scribbledlife/boardkey/images/3D view for keybaord.png

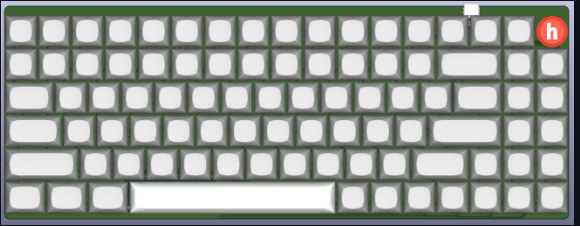
images/3D view for keybaord.png
