scribbledlife/boardkey/items/Screenshot 2026-02-18 142928.png

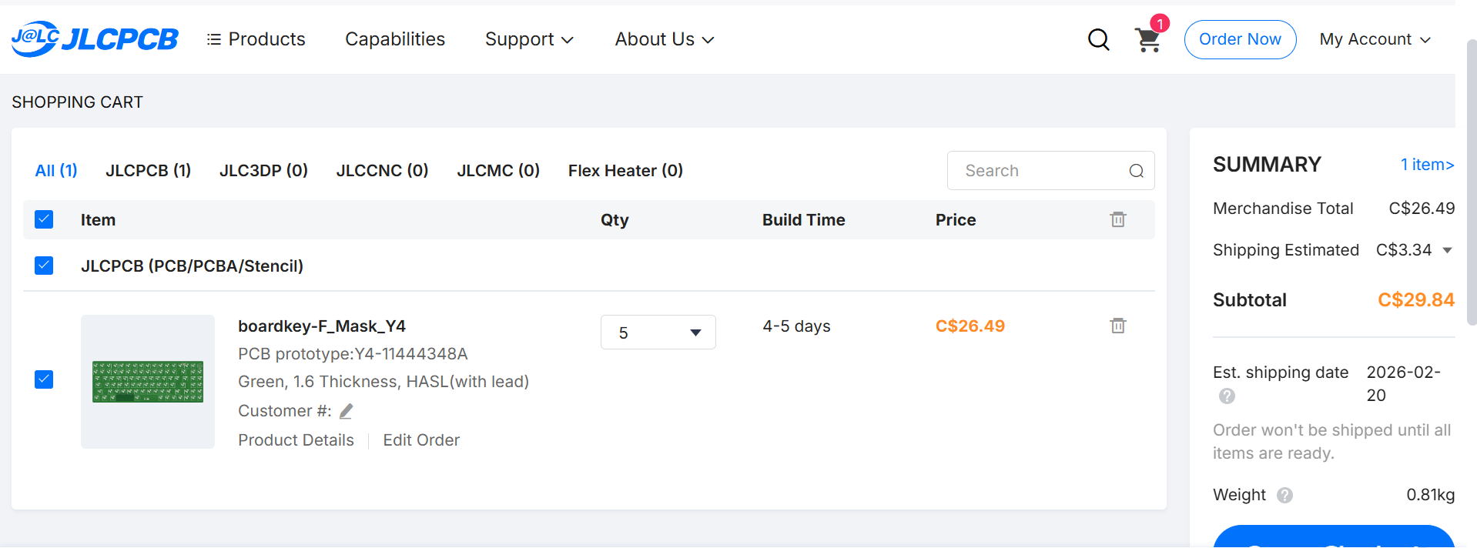
items/Screenshot 2026-02-18 142928.png
