scribbledlife/boardkey/items/Screenshot 2026-02-18 143510.png

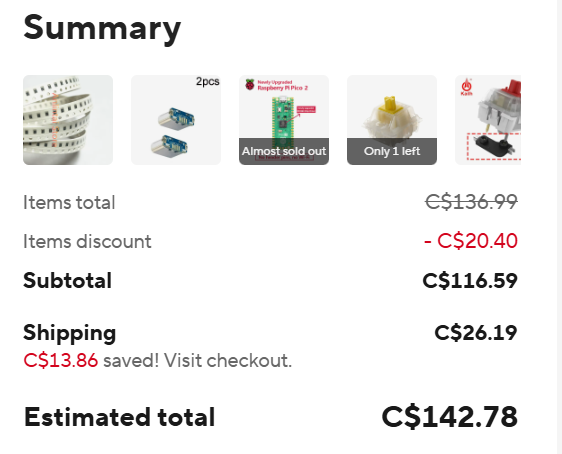
items/Screenshot 2026-02-18 143510.png
