scribbledlife/boardkey/items/Screenshot 2026-02-18 143522.png

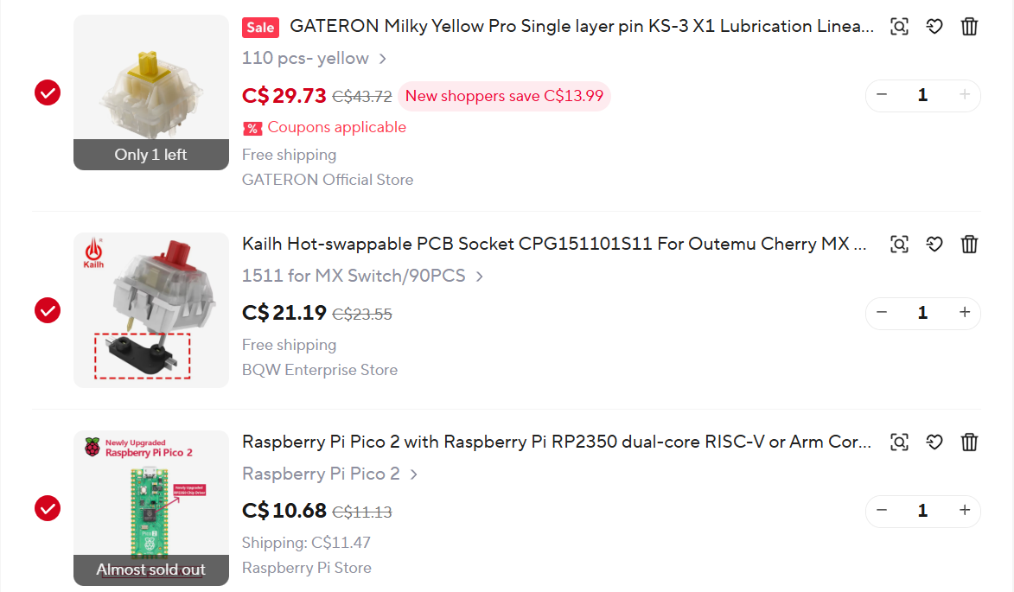
items/Screenshot 2026-02-18 143522.png
