scribbledlife/boardkey/items/Screenshot 2026-02-18 143550.png

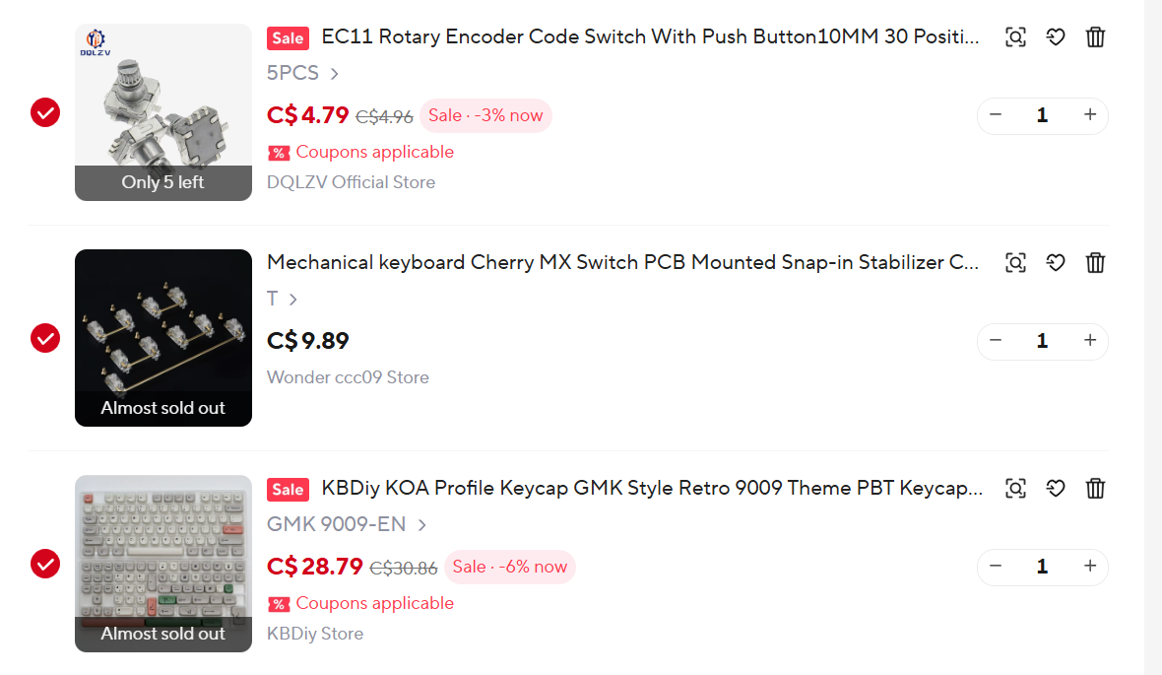
items/Screenshot 2026-02-18 143550.png
